ADElectronics/USB-Serial/Firmware/Src/newlib_cb.c

#include "main.h"

void _close(void)
{

}

void _lseek(void)
{

}

void _read(void)
{

}

#if(DEBUG_SEGGER_ENABLE == 0)
void _write(void)
{

}
#endif

void _fstat(void)
{

}

void _getpid(void)
{

}

void _isatty(void)
{

}

void _kill(void)
{

}
